DavesKosmoModules/Farini-VC-ADSR/Docs/20211023_091046.jpg

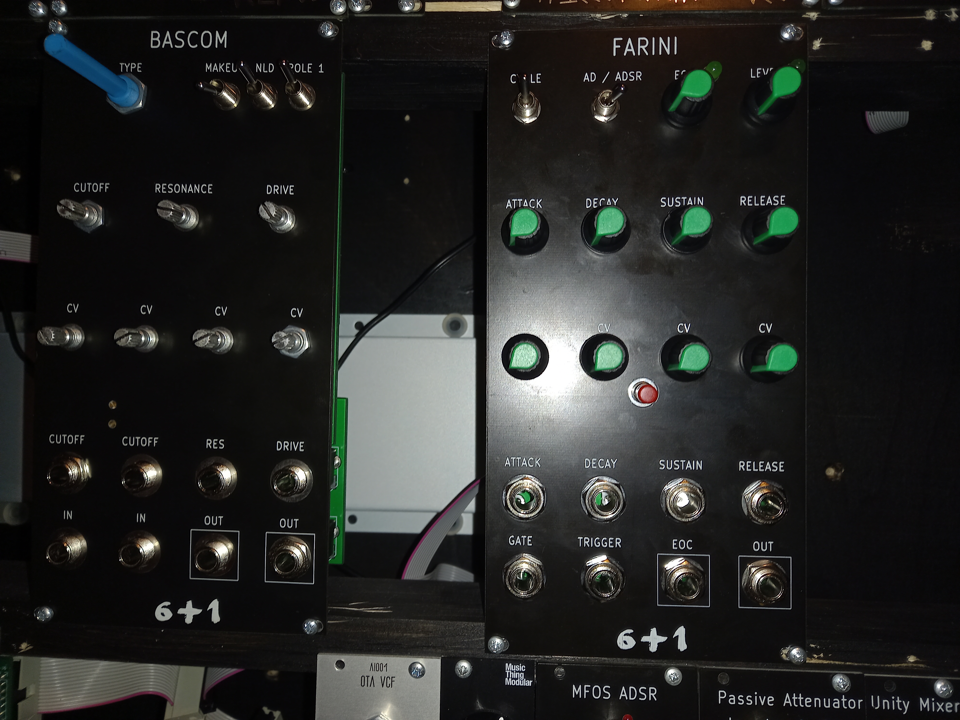
Docs/20211023_091046.jpg
